Lightwell-bg/LEDPixelClock/ClockLEDPixel/src/fwareupd.h

size_t content_len;

void handleDoUpdate(AsyncWebServerRequest *request, const String& filename, size_t index, uint8_t *data, size_t len, bool final) {
  if (!index) {
    Serial.println("Update");
    content_len = request->contentLength();
    // if filename includes spiffs, update the spiffs partition
    int cmd = (filename.indexOf("spiffs") > -1) ? 100 : 0; //U_SPIFFS : U_FLASH;
    Update.runAsync(true);
    if (!Update.begin(content_len, cmd)) {
      Update.printError(Serial);
    }
  }

  if (Update.write(data, len) != len) {
    Update.printError(Serial);
  }
  else {
    Serial.printf("Progress: %d%%\n", (Update.progress()*100)/Update.size());
  }

  if (final) {
    AsyncWebServerResponse *response = request->beginResponse(302, "text/plain", "Please wait while the device reboots");
    response->addHeader("Refresh", "20");  
    response->addHeader("Location", "/");
    request->send(response);
    if (!Update.end(true)){
      Update.printError(Serial);
    } else {
      Serial.println("Update complete");
      Serial.flush();
      ESP.restart();
    }
  }
}


void printProgress(size_t prg, size_t sz) {
  Serial.printf("Progress: %d%%\n", (prg*100)/content_len);
}

void init_firmWareUpdate(void) {
  HTTP.on("/doUpdate", HTTP_POST,
    [](AsyncWebServerRequest *request) {},
    [](AsyncWebServerRequest *request, const String& filename, size_t index, uint8_t *data,
                  size_t len, bool final) {handleDoUpdate(request, filename, index, data, len, final);}
  );
}
